Siggeaxe/Radiostyrd-bil/Bilder/Bil.jpg

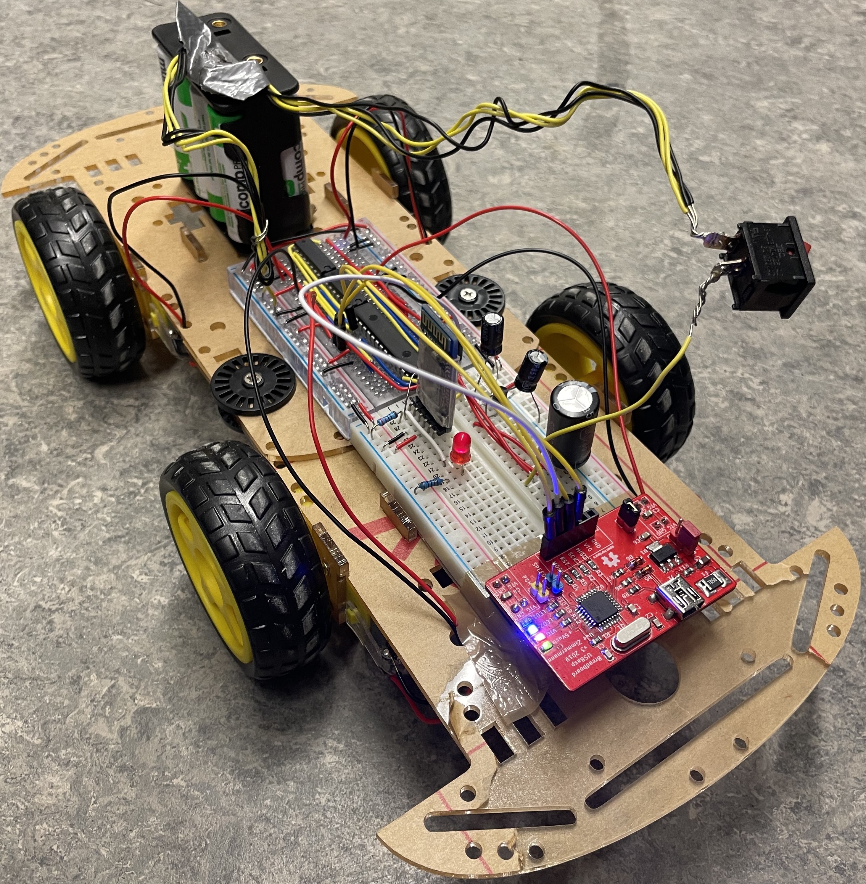
Bilder/Bil.jpg
