Siggeaxe/Radiostyrd-bil/Bilder/sn754410-320x320.png

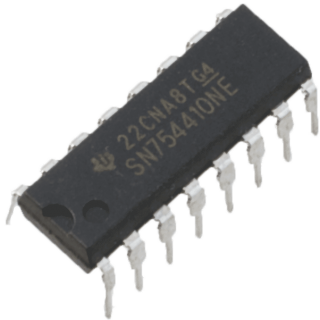
Bilder/sn754410-320x320.png
